FuturePresentLabs/legion-of-bom/crates/core/src/layout.rs

//! Iterative layout loop — place → route → check → repair (DESIGN.md §6.5).
//!
//! Not general autorouting: guided repair over the *free* (non-anchored) parts
//! only. Placement is the lever. [`SeededPlacer`](crate::board::SeededPlacer)
//! seeds each free part at the centroid of what it's netted to, so signal traces
//! stay short; this loop wraps that with a mode-weighted cost function, keeps the
//! best-scoring attempt, and — when the router still can't connect everything —
//! **repairs** by perturbing the implicated parts and trying again. It exits by
//! resolving what it can and *surfacing the rest for manual routing* (§6.8),
//! never silently forcing a net through.
//!
//! The per-iteration "check" is in-process (wirelength, via count, unrouted
//! conflicts, critical-net tightness) because a full KiCad DRC costs seconds per
//! run — too slow to score every attempt. KiCad DRC runs once, on the winning
//! board, as a final gate (`kicad_cli`), with an opt-in (`drc_every_iter`) to
//! fold it into every iteration when the caller accepts the cost.

use std::collections::HashMap;
use std::path::PathBuf;

use crate::board::{generate_board_artifacts, BoardError, BoardOptions, Placement, SeededPlacer};
use crate::drc::{run_drc, DrcReport};
use crate::route::RouteOutput;
use crate::source::CircuitSource;
use crate::stage::Finding;

/// Project layout mode (DESIGN §6.3) — selects the cost-function weights. Manual,
/// not auto-detected.
#[derive(Debug, Clone, Copy, PartialEq, Eq, Default)]
pub enum LayoutMode {
    /// Weights critical-net tightness and short signal wiring — audio boards.
    #[default]
    Analog,
    /// Weights via count and total routed length.
    Digital,
    /// Both, leaning on per-net `critical()` tags to disambiguate.
    Mixed,
}
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
